crmaykish/mackerel-68k/media/images/cbr_refresh_timing.png

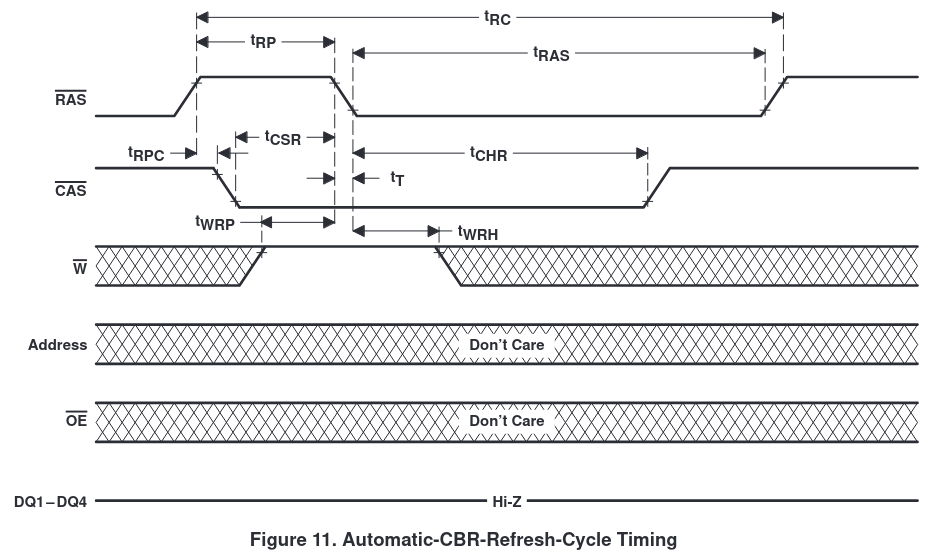
media/images/cbr_refresh_timing.png
