crmaykish/mackerel-68k/media/images/cbr_scope.png

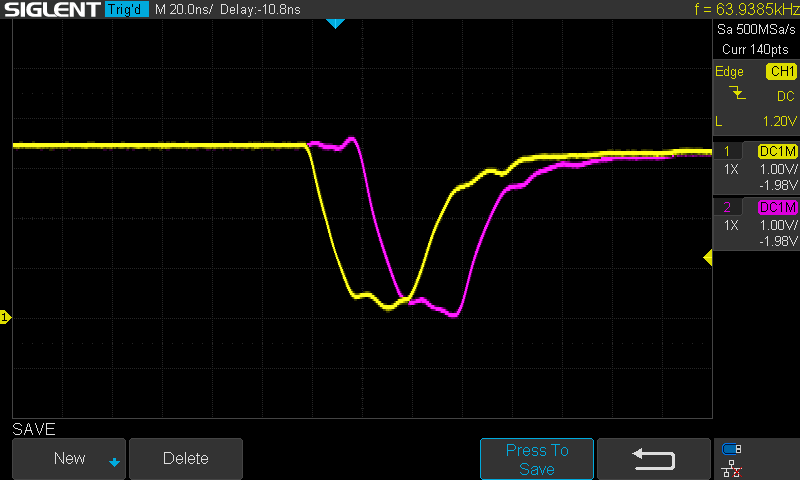
media/images/cbr_scope.png
