crmaykish/mackerel-68k/media/images/dram-cbr-refresh-simulation.png

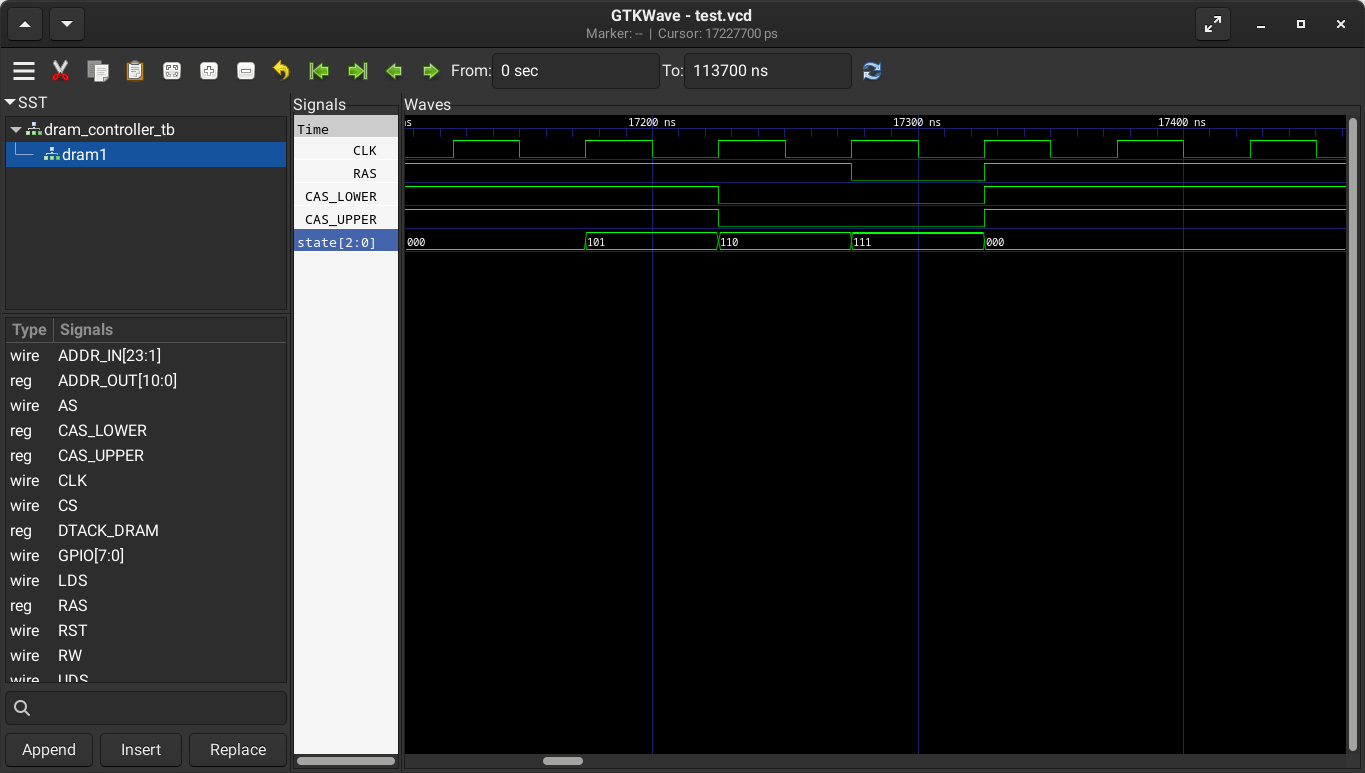
media/images/dram-cbr-refresh-simulation.png
