crmaykish/mackerel-68k/media/images/mack10_ide_proto.jpg

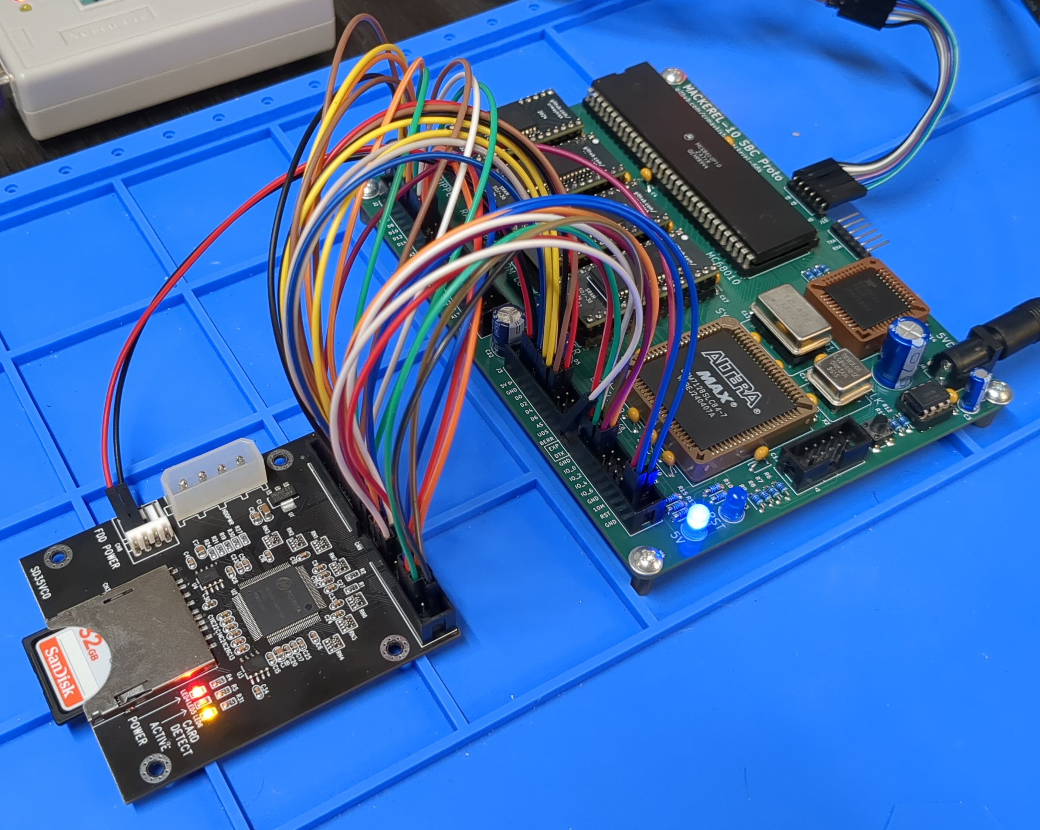
media/images/mack10_ide_proto.jpg
