crmaykish/mackerel-68k/media/images/mack-10-linux-mem-layout.png

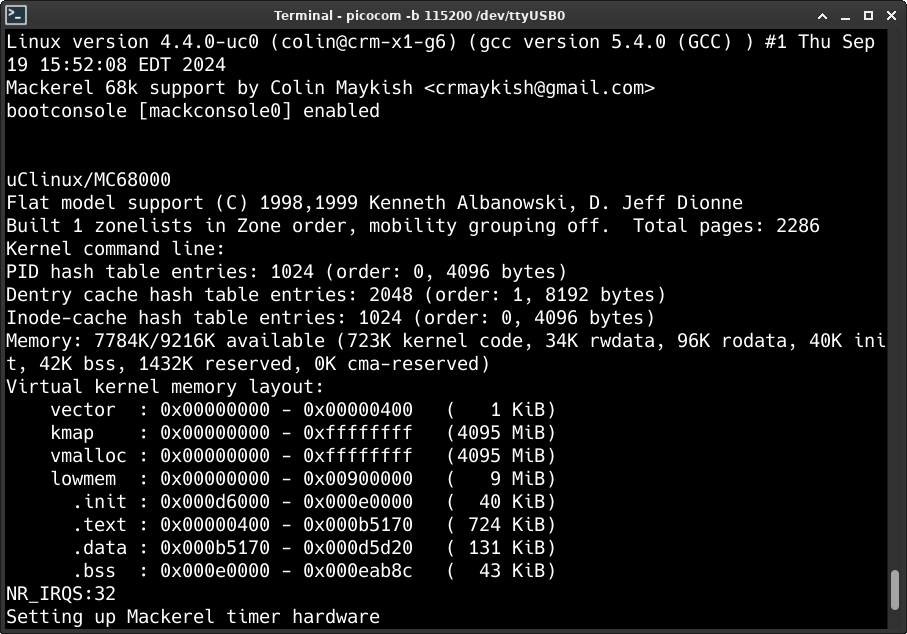
media/images/mack-10-linux-mem-layout.png
