crmaykish/mackerel-68k/media/images/mack-10-v1-routing.png

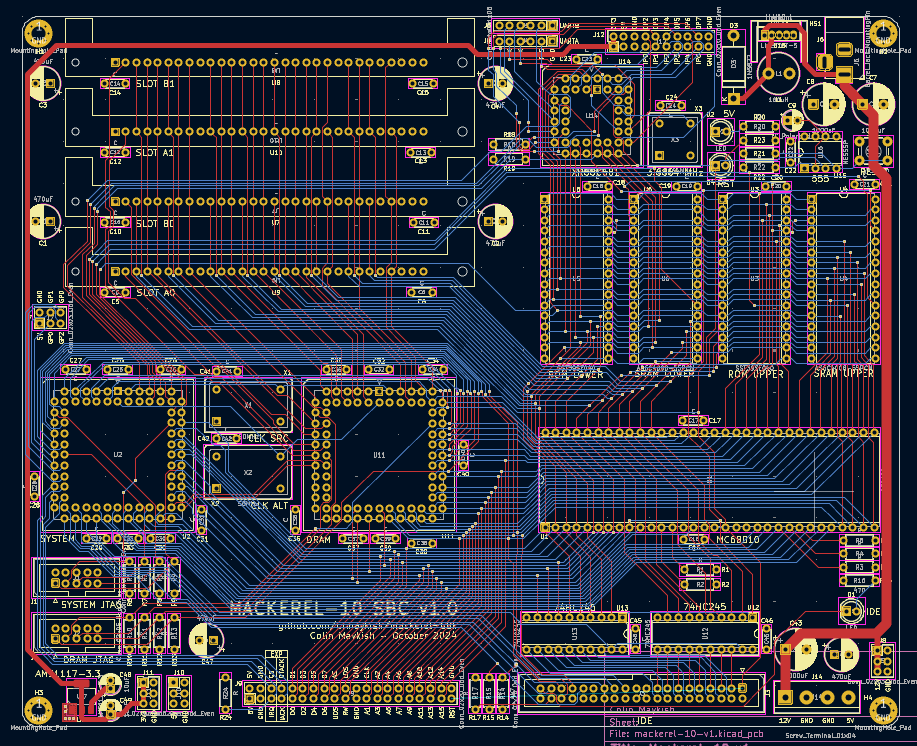
media/images/mack-10-v1-routing.png
