crmaykish/mackerel-68k/media/images/mackerel-08-rev0.jpg

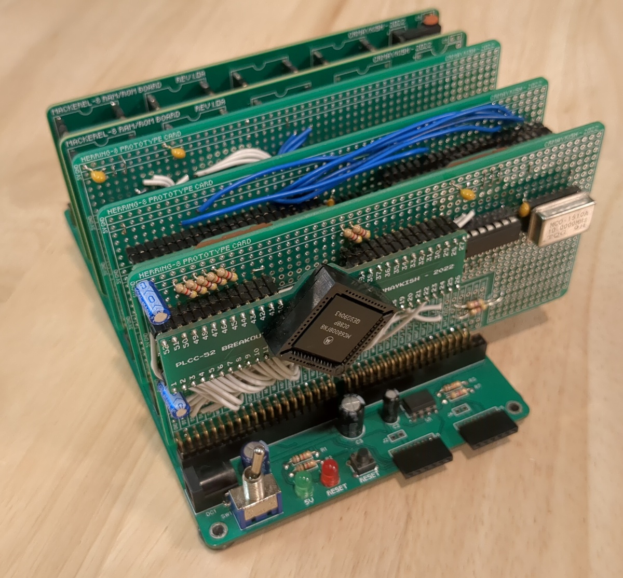
media/images/mackerel-08-rev0.jpg
