crmaykish/mackerel-68k/media/images/mackerel-08-rev1.1.jpg

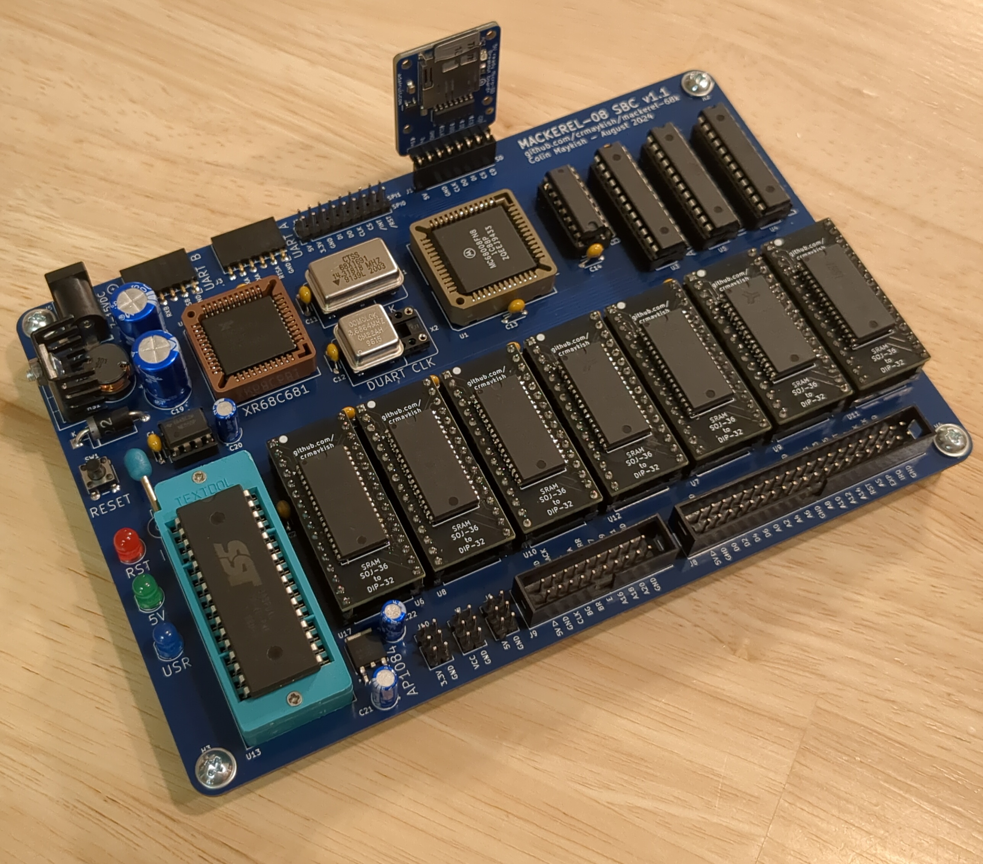
media/images/mackerel-08-rev1.1.jpg
