crmaykish/mackerel-68k/media/images/mackerel-08-sbc-v1-routing.png

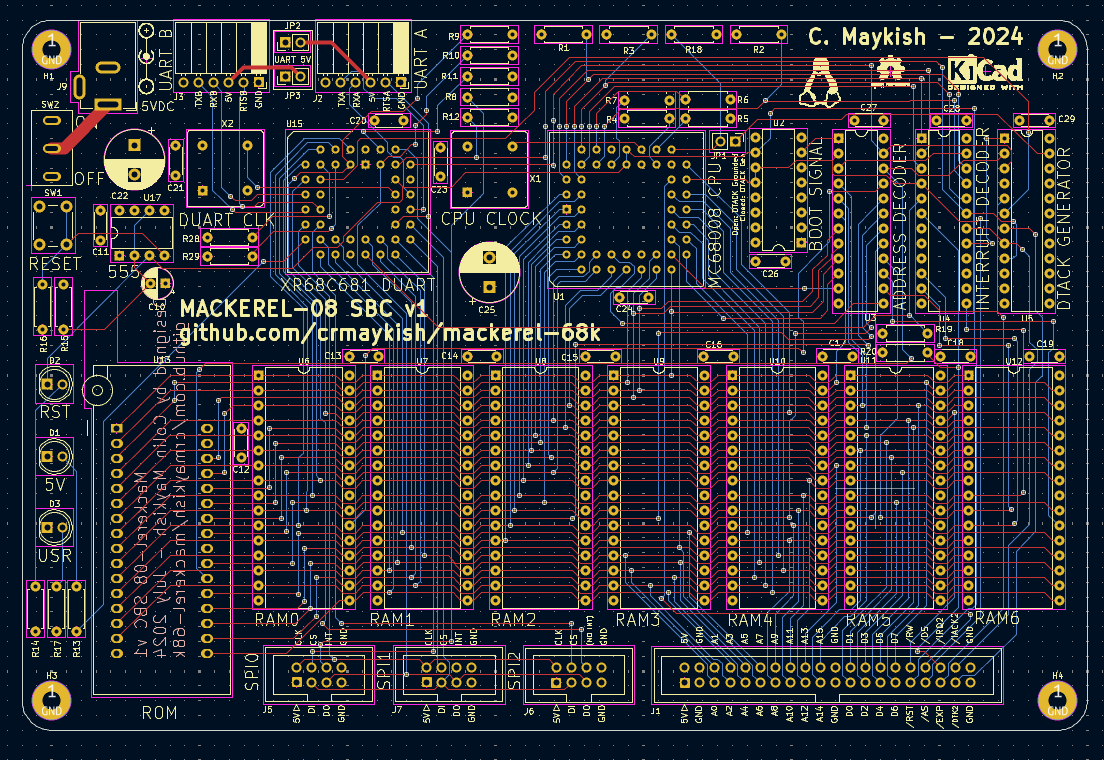
media/images/mackerel-08-sbc-v1-routing.png
