crmaykish/mackerel-68k/media/images/mackerel-08-sbc-v1.1-render.png

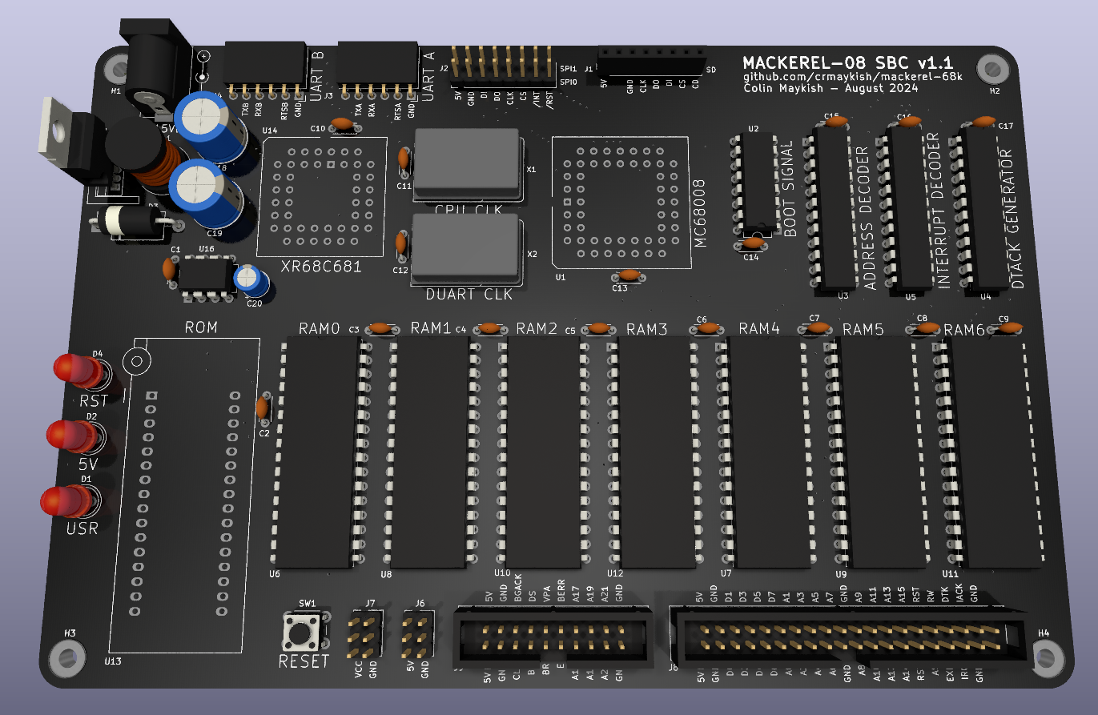
media/images/mackerel-08-sbc-v1.1-render.png
