crmaykish/mackerel-68k/media/images/mackerel-10-proto.jpg

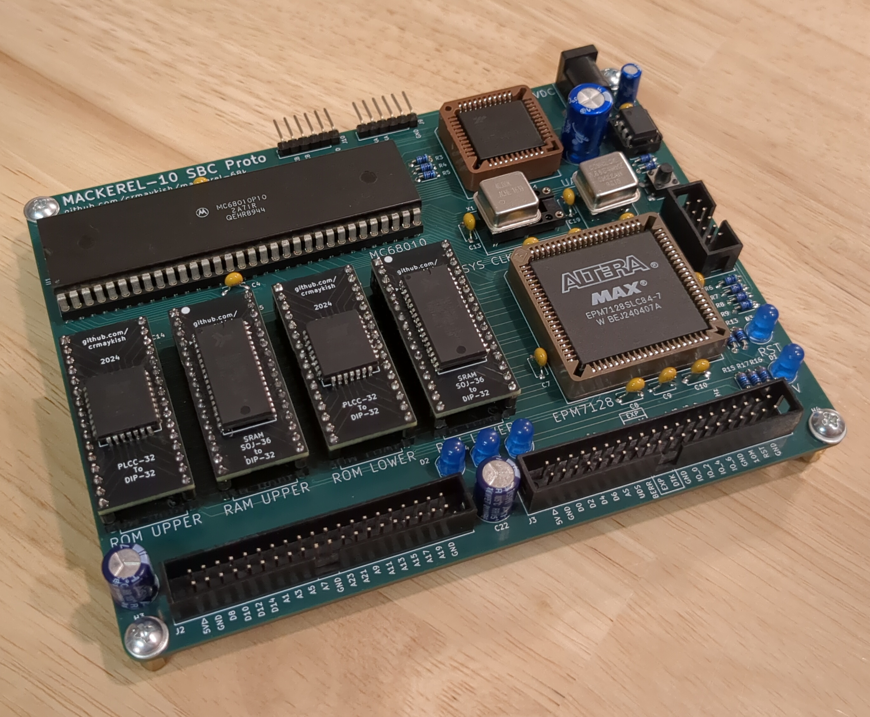
media/images/mackerel-10-proto.jpg
