crmaykish/mackerel-68k/media/images/mackerel-10-sbc-proto-render.png

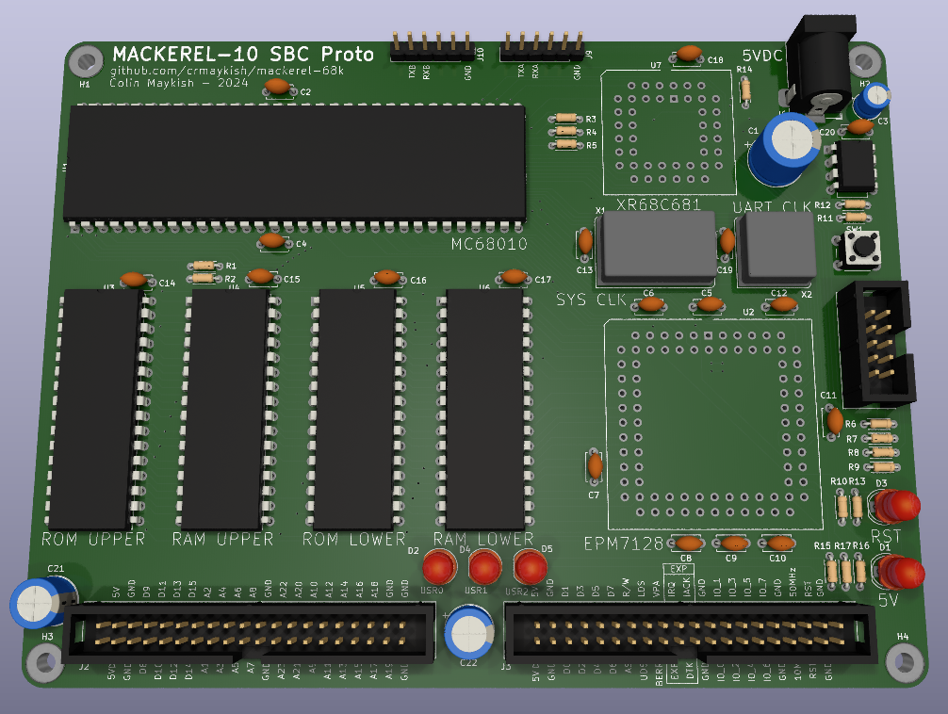
media/images/mackerel-10-sbc-proto-render.png
