crmaykish/mackerel-68k/media/images/mackerel-10-v1-with-drive.jpg

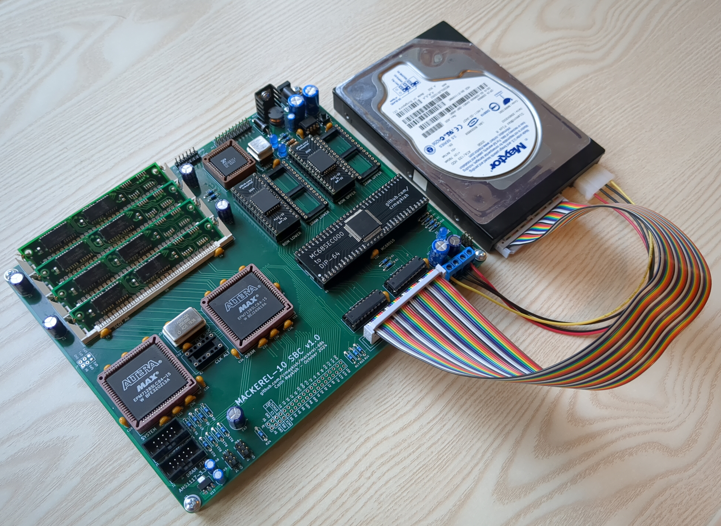
media/images/mackerel-10-v1-with-drive.jpg
