crmaykish/mackerel-68k/media/images/mackerel-30-v0.1-routing.png

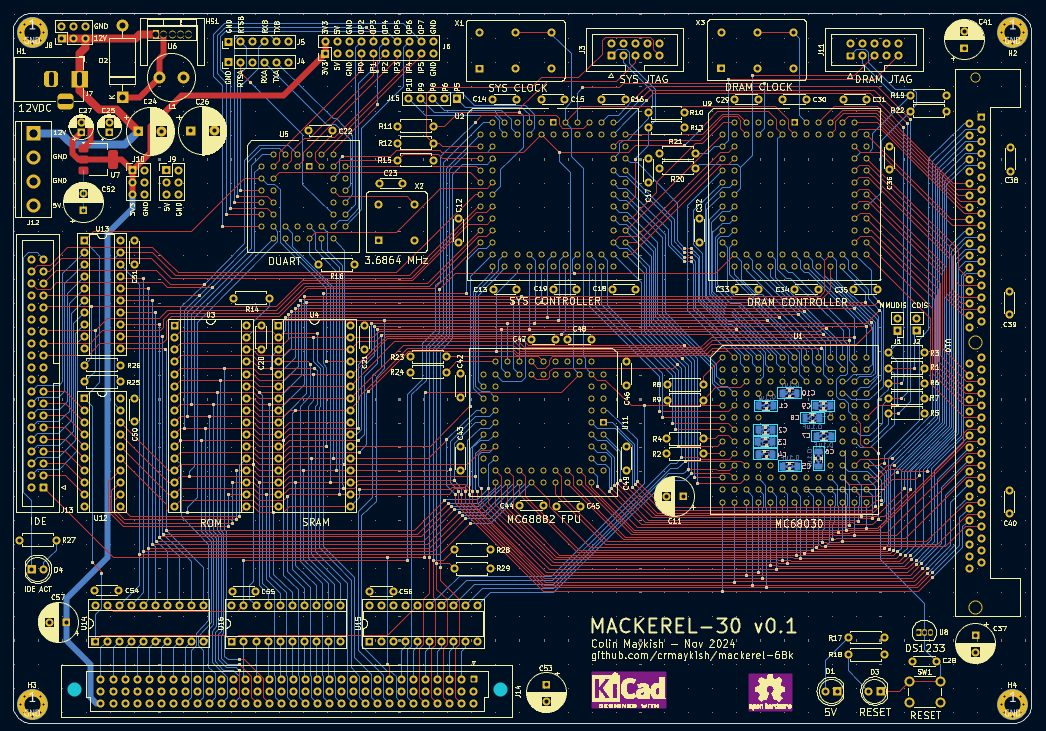
media/images/mackerel-30-v0.1-routing.png
