crmaykish/mackerel-68k/media/images/mackerel-f.png

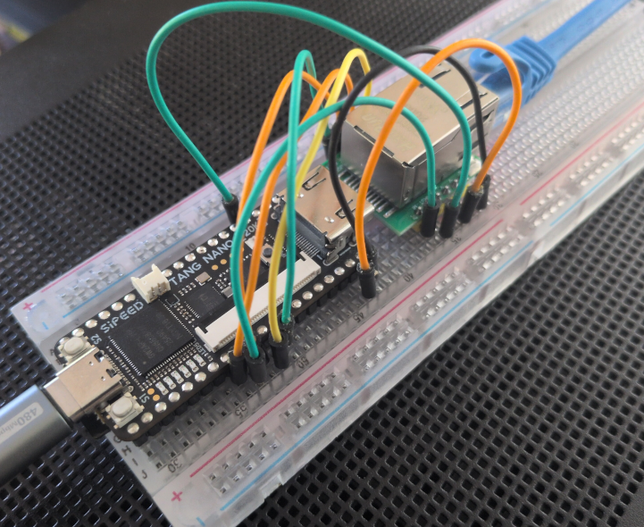
media/images/mackerel-f.png
