crmaykish/mackerel-68k/media/images/mackerel-08-sbc-v1-board-bringup.jpg

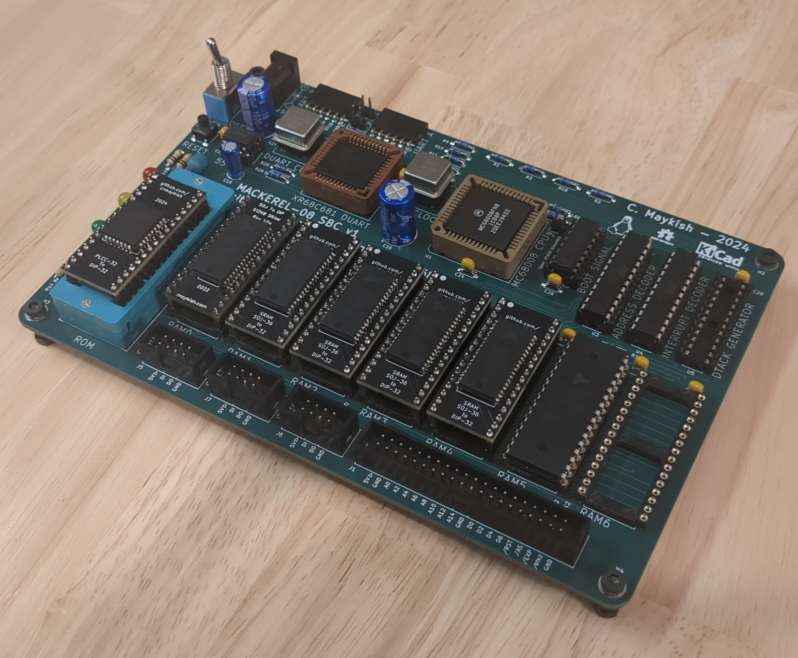
media/images/mackerel-08-sbc-v1-board-bringup.jpg
