crmaykish/mackerel-68k/media/images/mackerel-30-v0.1-bringup.jpg

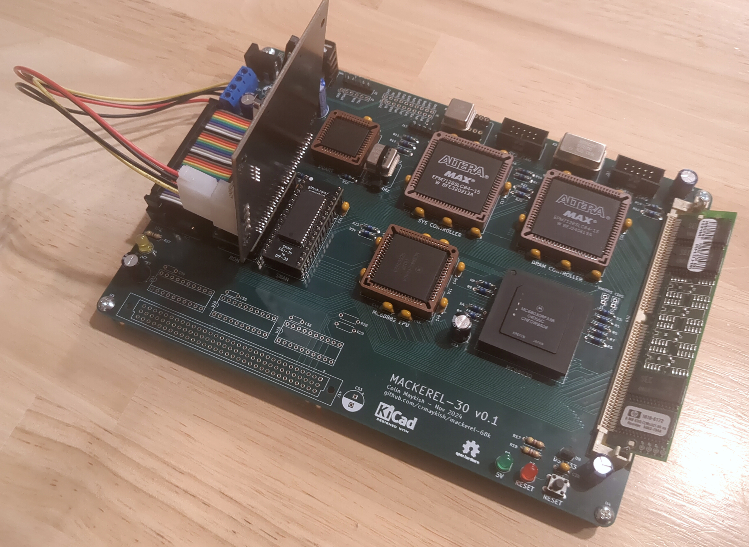
media/images/mackerel-30-v0.1-bringup.jpg
