crmaykish/mackerel-68k/pld/mackerel-30/system_controller/system_controller.v

module system_controller(
	input RST_n,
	input CLK,

	input [31:28] AH,	// Address bus (high)
	input [19:16] AM,	// Address bus (mid)
	input [3:0] AL,		// Address bus (low)

	output reg DSACK0_n, DSACK1_n,
	output BERR_n,
	output reg AVEC_n = 1'b1,
	output CIIN_n,
	output STERM_n,

	input [2:0] FC,
	output [2:0] IPL_n,
	
	input AS_n, DS_n,
	input SIZ0, SIZ1,
	input RW,
	
	output CS_ROM_n,
	output CS_SRAM_n,
	
	output CS_DRAM_n,
	input DSACK0_DRAM_n,
	input DSACK1_DRAM_n,

	output CS_FPU_n,
	input DSACK0_FPU_n,
	input DSACK1_FPU_n,
	
	output CS_DUART_n,
	output IACK_DUART_n,
	input IRQ_DUART_n,
	input DTACK_DUART_n,
	
	output IDE_BUF_n,
	output IDE_CS0_n,
	output IDE_CS1_n,
	output IDE_WR_n,
	output IDE_RD_n,
	input IDE_RDY,
	input IDE_INT,
	
	output EXP_BUF_n,
	output P5, P6, P8, P9,

	input ENC_INT_n
);

// === COMMON SIGNALS === //

// Processor is addressing CPU space
wire CPU_SPACE = (FC == 3'b111);
// Processor is responding to an interrupt
wire IACK_n = ~(CPU_SPACE && ~AS_n && AM[19:16] == 4'b1111);

// SRAM address space: 0xC0000000
wire SRAM_SPACE = (AH == 4'b1100);
// DRAM address space: 0x00000000
wire DRAM_SPACE = (AH == 4'b0000);
// ROM address space: 0xE0000000
wire ROM_SPACE = (AH == 4'b1110);
// I/O address space: 0xF0000000
wire IO_SPACE = (AH == 4'b1111);

// Coprocessor cycle — used for both CS_FPU_n and DSACK routing
wire COP_CYCLE = CPU_SPACE && ~AS_n && (AM == 4'b0010);

// Tie BERR high - bus errors will just hang the CPU
assign BERR_n = 1'b1;

// Inhibit cache for I/O
assign CIIN_n = ~(~CPU_SPACE && ~AS_n && (IO_SPACE));
assign STERM_n = 1'b1;

// === BOOT SIGNAL === //

wire BOOT;
boot_signal bs(RST_n, AS_n, BOOT);

// DUART IACK is mapped to IRQ level 5
assign IACK_DUART_n = ~(~IACK_n && AL[3:1] == 3'd5);

// === ADDRESS DECODING === //

// ROM at 0xE0000000 (mapped to 0x0000 for the first eight bus cycles)
wire ROM_EN = ~BOOT || (AH == 4'b1110);
assign CS_ROM_n = ~(~CPU_SPACE && ~AS_n && ROM_EN);

assign CS_SRAM_n = ~(BOOT && ~CPU_SPACE && ~AS_n && ~DS_n && AH == 4'b1100);

// DRAM at 0x0000_0000 - 0x7FFF_FFFF
assign CS_DRAM_n = ~(BOOT && ~CPU_SPACE && AH == 4'b0000);
// assign CS_DRAM_n = 1'b1;

// DUART at 0xF0000000
assign CS_DUART_n = ~(BOOT && ~CPU_SPACE && ~AS_n && ~DS_n && IO_SPACE && AM == 4'b0000);

// IDE CS0 at 0xF0010000
assign IDE_CS0_n = ~(BOOT && ~CPU_SPACE && IO_SPACE && AM == 4'b0001);
// IDE CS1 at 0xF0020000
assign IDE_CS1_n = ~(BOOT && ~CPU_SPACE && IO_SPACE && AM == 4'b0010);

// Timer control registers at 0xF0030000
wire CS_TIMER_n;
assign CS_TIMER_n = ~(BOOT && ~CPU_SPACE && ~AS_n && ~DS_n && IO_SPACE && AM == 4'b0011);

// IDE is selected if either CS0 or CS1 is active
wire CS_IDE_n = ~(~AS_n && (~IDE_CS0_n || ~IDE_CS1_n));

assign IDE_BUF_n = CS_IDE_n;
assign IDE_RD_n = ~(RW && ~AS_n && ~DS_n);
assign IDE_WR_n = ~(~RW && ~AS_n && ~DS_n);

// TODO: Expansion buffer currently not supported
assign EXP_BUF_n = 1'b1;

// CS_FPU_n gated by AS_n (same as COP_CYCLE) to prevent spurious assertions
// between bus cycles when FC/AM transiently pass through coprocessor values.
assign CS_FPU_n = ~COP_CYCLE;

// === WAIT STATE GENERATION === //

// PIO mode 0 minimum cycle time is 600 ns; at 24 MHz (41.7 ns/cycle) that
// requires ~14 wait clocks.  The ide_waiting pulse is held for IDE_WAIT+1
// cycles, so IDE_WAIT=14 gives 15 cycles (~625 ns)
parameter IDE_WAIT  = 14;  // IDE wait states (cycles)
parameter DUART_WAIT = 0;  // DUART wait states (cycles)

reg [3:0] ide_wait_cnt = 0;
reg [3:0] duart_wait_cnt = 0;
reg ide_waiting = 0;
reg duart_waiting = 0;

// Clocked wait-state generator
always @(posedge CLK or negedge RST_n) begin
    if (!RST_n) begin
        ide_wait_cnt <= 0;
		ide_waiting <= 0;
        duart_wait_cnt <= 0;
        duart_waiting <= 0;
    end
	else begin
        // IDE wait state logic
        if (~CS_IDE_n && ~ide_waiting) begin
            ide_wait_cnt <= 0;
            ide_waiting <= 1;
        end else if (ide_waiting && ide_wait_cnt < IDE_WAIT) begin
            ide_wait_cnt <= ide_wait_cnt + 1;
        end else if (ide_waiting && ide_wait_cnt >= IDE_WAIT) begin
            ide_waiting <= 0;
        end

        // DUART wait state logic
        if (~CS_DUART_n && ~duart_waiting) begin
            duart_wait_cnt <= 0;
            duart_waiting <= 1;
        end else if (duart_waiting && duart_wait_cnt < DUART_WAIT) begin
            duart_wait_cnt <= duart_wait_cnt + 1;
        end else if (duart_waiting && duart_wait_cnt >= DUART_WAIT) begin
            duart_waiting <= 0;
        end
    end
end

// === TIMER INTERRUPT === //
parameter integer CPU_CLK_HZ    = 24_000_000;
parameter integer TIMER_DIVIDER = CPU_CLK_HZ / 100;  // 100 Hz timer tick
reg [$clog2(TIMER_DIVIDER)-1:0] timer_cnt = 0;
reg timer_enable = 1'b0;
reg IRQ_TIMER = 1'b0;   // Timer interrupt flag

// Detect writes to enable / disable registers
wire timer_write = (~CS_TIMER_n && ~RW);  // active during write cycle
wire timer_en_write  = timer_write && (AL == 4'h0);
wire timer_dis_write = timer_write && (AL == 4'h1);

// Level 6 IACK detection (autovector) to clear pending
wire IACK_LVL6 = (~IACK_n && ~AS_n && AL[3:1] == 3'd6);

always @(posedge CLK or negedge RST_n) begin
    if (!RST_n) begin
        timer_cnt <= 0;
        timer_enable <= 1'b0;
        IRQ_TIMER <= 1'b0;
    end else begin
        // Register writes
        if (timer_en_write)
            timer_enable <= 1'b1;
        else if (timer_dis_write) begin
            timer_enable <= 1'b0;
            IRQ_TIMER <= 1'b0;
            timer_cnt <= 0;
        end

        // Counter / interrupt generation
        if (timer_enable) begin
            if (timer_cnt == TIMER_DIVIDER - 1) begin
                timer_cnt <= 0;
                IRQ_TIMER <= 1'b1;
            end else begin
                timer_cnt <= timer_cnt + 1;
            end
        end else begin
            timer_cnt <= 0;
        end

        // Clear on level 6 IACK
        if (IACK_LVL6)
            IRQ_TIMER <= 1'b0;
    end
end

// === ENC28J60 INTERRUPT (IPL 4) === //
// Edge-detecting latch: fires on falling edge of ENC_INT_n, clears on IACK
reg enc_int_prev = 1'b1;
reg IRQ_ENC      = 1'b0;
wire IACK_LVL4 = ~IACK_n && ~AS_n && AL[3:1] == 3'd4;

always @(posedge CLK or negedge RST_n) begin
    if (!RST_n) begin
        enc_int_prev <= 1'b1;
        IRQ_ENC      <= 1'b0;
    end else begin
        enc_int_prev <= ENC_INT_n;
        if (enc_int_prev && !ENC_INT_n)  // falling edge → latch
            IRQ_ENC <= 1'b1;
        else if (IACK_LVL4)              // IACK → clear
            IRQ_ENC <= 1'b0;
    end
end

// === INTERRUPT HANDLING === //

irq_encoder ie1(
	.irq1(0),
	.irq2(0),
	.irq3(IDE_INT),
	.irq4(0),   // TODO: Wire IRQ_ENC when ENC28J60 is installed
	.irq5(~IRQ_DUART_n),
	.irq6(IRQ_TIMER),
	.irq7(0),
	.ipl0_n(IPL_n[0]),
	.ipl1_n(IPL_n[1]),
	.ipl2_n(IPL_n[2])
);

// Autovector the non-DUART interrupts
always @(*) begin
    if (~IACK_n && IACK_DUART_n && ~AS_n)
        AVEC_n = 1'b0;
    else
        AVEC_n = 1'b1;
end

// === DSACK GENERATION === //
always @(*) begin
    // Handle interrupt acknowledge cycles
    if (~IACK_n) begin
        if (~IACK_DUART_n) begin
            DSACK0_n = 1'b0;
            DSACK1_n = 1'b1;
        end else begin
            // Autovector
            DSACK0_n = 1'b0;
            DSACK1_n = 1'b1;
        end
    end
    else if (~CS_DRAM_n) begin
        // Gate DRAM DSACK with AS
        if (~AS_n) begin
            DSACK0_n = DSACK0_DRAM_n;
            DSACK1_n = DSACK1_DRAM_n;
        end else begin
            DSACK0_n = 1'b1;
            DSACK1_n = 1'b1;
        end
    end
    else if (~CS_IDE_n) begin
        // Insert IDE wait states before asserting DSACK
        if (ide_waiting) begin
            DSACK0_n = 1'b1;
            DSACK1_n = 1'b1;
        end
        else begin
            DSACK0_n = 1'b1;
            DSACK1_n = 1'b0;
        end
    end
    else if (~CS_DUART_n) begin
        // Insert DUART wait states before asserting DSACK
        if (duart_waiting) begin
            DSACK0_n = 1'b1;
            DSACK1_n = 1'b1;
        end
        else begin
            DSACK0_n = 1'b0;
            DSACK1_n = 1'b1;
        end
    end
    else if (~CS_TIMER_n) begin
        // Timer registers respond immediately
        DSACK0_n = 1'b0;
        DSACK1_n = 1'b1;
    end
    else if (~CS_ROM_n || ~CS_SRAM_n) begin
        DSACK0_n = 1'b0;
        DSACK1_n = 1'b1;
    end
    else if (~CS_FPU_n) begin
        DSACK0_n = DSACK0_FPU_n;
        DSACK1_n = DSACK1_FPU_n;
    end
    else begin
        DSACK0_n = 1'b1;
        DSACK1_n = 1'b1;
    end
end

endmodule
