crmaykish/mackerel-68k/firmware/fat16.c

#include <stdio.h>
#include <string.h>
#include "fat16.h"
#include "term.h"
#include "console.h"

fat16_read_sector_f read_sector = NULL;

// Start LBA of the FAT16 partition. Defaults to 2048 (the conventional 1 MB offset)
static uint32_t fat16_part_lba = 2048;

uint32_t fat16_part_start(void) { return fat16_part_lba; }

// Read the MBR (LBA 0) and locate the first FAT16 partition, setting the start
// LBA used by the rest of the library. Returns 0 if one was found, -1 otherwise
int fat16_find_partition(void)
{
    if (read_sector == NULL)
        return -1;

    uint8_t mbr[512];
    if (read_sector(0, mbr, 1) != 0)
        return -1;
    if (mbr[510] != 0x55 || mbr[511] != 0xAA)   // boot signature
        return -1;

    for (int i = 0; i < 4; i++)
    {
        const uint8_t *e = mbr + 0x1BE + i * 16;
        uint8_t type = e[4];
        // FAT16: 0x04 (<32MB), 0x06 (FAT16B), 0x0E (FAT16 LBA)
        if (type == 0x04 || type == 0x06 || type == 0x0E)
        {
            fat16_part_lba = (uint32_t)e[8] | ((uint32_t)e[9] << 8) | ((uint32_t)e[10] << 16) | ((uint32_t)e[11] << 24);
            return 0;
        }
    }
    return -1;
}

void bswap_boot_sector(fat16_boot_sector_t *b)
{
    if (b == NULL)
        return;

    b->bytes_per_sector = bswap16(b->bytes_per_sector);
    b->reserved_sectors = bswap16(b->reserved_sectors);
    b->root_entries = bswap16(b->root_entries);
    b->total_sectors_16 = bswap16(b->total_sectors_16);
    b->fat_size_16 = bswap16(b->fat_size_16);
    b->sectors_per_track = bswap16(b->sectors_per_track);
    b->heads = bswap16(b->heads);
    b->hidden_sectors = bswap32(b->hidden_sectors);
    b->total_sectors_32 = bswap32(b->total_sectors_32);
    b->volume_id = bswap32(b->volume_id);
    b->boot_sector_signature = bswap16(b->boot_sector_signature);
}

void bswap_dir_entry(fat16_dir_entry_t *d)
{
    if (d == NULL)
        return;

    d->creation_time = bswap16(d->creation_time);
    d->creation_date = bswap16(d->creation_date);
    d->last_access_date = bswap16(d->last_access_date);
    d->first_cluster_high = bswap16(d->first_cluster_high);
    d->modification_time = bswap16(d->modification_time);
    d->modification_date = bswap16(d->modification_date);
    d->first_cluster_low = bswap16(d->first_cluster_low);
    d->file_size = bswap32(d->file_size);
}

int fat16_init(fat16_read_sector_f read_sector_fun)
{
    if (read_sector_fun)
    {
        read_sector = read_sector_fun;
        return 0;
    }

    return -1;
}

void fat16_read_boot_sector(uint32_t starting_sector, fat16_boot_sector_t *buffer)
{
    read_sector(starting_sector, (uint8_t *)(buffer), 1);
    bswap_boot_sector(buffer);
}

void fat16_print_boot_sector_info(fat16_boot_sector_t *buffer)
{
    printf("\r\nBoot sector info:\r\n");
    printf("Bytes per sector: %u\n", buffer->bytes_per_sector);
    printf("Sectors per cluster: %u\n", buffer->sectors_per_cluster);
    printf("Reserved sectors: %u\n", buffer->reserved_sectors);
    printf("FAT count: %u\n", buffer->num_fats);
    printf("Root directory entries: %u\n", buffer->root_entries);
    printf("Total sectors: %u\n", buffer->total_sectors_16);
    printf("FAT size (sectors): %u\n", buffer->fat_size_16);
    printf("Sectors per track: %u\n", buffer->sectors_per_track);
    printf("Head count: %u\n", buffer->heads);
    printf("Hidden sectors: %lu\n", buffer->hidden_sectors);
    printf("Total sectors (large): %lu\n", buffer->total_sectors_32);
}

int fat16_list_files(fat16_boot_sector_t *boot_sector, fat16_dir_entry_t files_list[])
{
    if (read_sector == NULL)
    {
        printf("read_sector function pointer is NULL. Call fat16_init() first\r\n");
        return -1;
    }

    if (boot_sector == NULL)
    {
        printf("boot_sector is NULL\r\n");
        return -1;
    }

    int valid_files = 0;

    uint32_t root_dir_sector = fat16_part_lba + boot_sector->reserved_sectors + (boot_sector->num_fats * boot_sector->fat_size_16);
    uint8_t buffer[512];

    read_sector(root_dir_sector, buffer, 1);

    // TODO: this 16 value should be determined by the root directory count in the boot sector
    // After 16 entries, a new sector needs to be read (I think)
    for (int i = 0; i < 16; i++)
    {
        fat16_dir_entry_t *entry = (fat16_dir_entry_t *)(buffer + i * 32);

        bswap_dir_entry(entry);

        // Check if the entry is free (0x00) or deleted (0xE5)
        if (entry->filename[0] == 0x00 || entry->filename[0] == 0xE5)
        {
            continue; // Skip empty or deleted entries
        }

        // Check if the entry represents a valid file or directory
        if (entry->attributes & 0x10)
        {
            // This is a directory (attribute 0x10)
            continue;
        }

        memcpy(&files_list[valid_files], entry, 32);
        valid_files++;
    }

    return valid_files;
}

void fat16_get_file_name(fat16_dir_entry_t *dir_entry, char *filename)
{
    if (dir_entry == NULL)
    {
        return;
    }

    if (filename == NULL)
    {
        return;
    }

    memset(filename, ' ', 13);

    // Copy the name
    strncpy(filename, (char *)dir_entry->filename, 8);
    // Add a dot between the name and extension
    filename[8] = '.';
    // Copy the extension
    strncpy(filename + 9, (char *)dir_entry->extension, 3);

    filename[12] = 0; // Null-terminate the string
}

// Function to get the next cluster from the FAT
uint16_t get_fat_entry(fat16_boot_sector_t *boot_sector, uint16_t cluster)
{
    static uint32_t cached_sector = (uint32_t)-1;
    static uint8_t fat_buffer[1024]; // Make sure this is large enough for your largest sector size

    uint32_t fat_offset = cluster * 2;
    uint32_t fat_sector = boot_sector->hidden_sectors + boot_sector->reserved_sectors + (fat_offset / boot_sector->bytes_per_sector);
    uint32_t fat_entry_offset = fat_offset % boot_sector->bytes_per_sector;

    // Only read if not already cached
    if (fat_sector != cached_sector) {
        if (read_sector(fat_sector, fat_buffer, 1) != 0)
            return 0xFFFF;  // treat read failure as end-of-chain
        cached_sector = fat_sector;
    }

    uint16_t next_cluster = (fat_buffer[fat_entry_offset] | (fat_buffer[fat_entry_offset + 1] << 8)) & 0xFFFF;
    return next_cluster;
}

int fat16_read_file(fat16_boot_sector_t *boot_sector, uint16_t starting_cluster, uint8_t *buffer, uint32_t buffer_size)
{
    uint32_t buffer_index = 0;
    uint16_t current_cluster = starting_cluster;

    // Calculate the first sector of the cluster
    uint32_t sector_size = boot_sector->bytes_per_sector;
    uint32_t sectors_per_cluster = boot_sector->sectors_per_cluster;

    // Progress reporting
    uint32_t pct_step = buffer_size / 100;
    if (pct_step == 0)
        pct_step = 1;
    int last_pct = -1;

    // Hide the cursor while the progress bar redraws to keep it from
    // flickering across the bar. Re-enabled on every exit path below.
    term_cursor_set_vis(false);

    uint32_t root_dir_sectors = (boot_sector->root_entries * 32 + sector_size - 1) / sector_size;

    while (current_cluster != 0xFFFF && buffer_index < buffer_size)
    {
        // printf("current cluster: %u\r\n", current_cluster);

        uint32_t first_sector_of_cluster = root_dir_sectors + fat16_part_lba + (current_cluster - 2) * sectors_per_cluster + boot_sector->reserved_sectors + (boot_sector->num_fats * boot_sector->fat_size_16);

        // Read the sectors of the current cluster into the buffer
        uint32_t remaining = buffer_size - buffer_index;
        uint32_t cluster_bytes = (uint32_t)sectors_per_cluster * sector_size;

        if (remaining >= cluster_bytes)
        {
            // Whole cluster fits — one multi-sector read straight into destination
            if (read_sector(first_sector_of_cluster, buffer + buffer_index, sectors_per_cluster) != 0)
            {
                term_cursor_set_vis(true);
                return -1;
            }
            buffer_index += cluster_bytes;
        }
        else
        {
            // Partial cluster at end of file — fall back to sector by sector
            for (uint32_t i = 0; i < sectors_per_cluster && buffer_index < buffer_size; i++)
            {
                uint32_t rem = buffer_size - buffer_index;
                if (rem >= sector_size)
                {
                    if (read_sector(first_sector_of_cluster + i, buffer + buffer_index, 1) != 0)
                    {
                        term_cursor_set_vis(true);
                        return -1;
                    }
                    buffer_index += sector_size;
                }
                else
                {
                    uint8_t sector_buffer[sector_size];
                    if (read_sector(first_sector_of_cluster + i, sector_buffer, 1) != 0)
                    {
                        term_cursor_set_vis(true);
                        return -1;
                    }
                    memcpy(buffer + buffer_index, sector_buffer, rem);
                    buffer_index += rem;
                }
            }
        }

        // Redraw the progress bar only when the percentage changes.
        int pct = buffer_index / pct_step;
        if (pct > 100)
            pct = 100;
        if (pct != last_pct)
        {
            last_pct = pct;
            term_progress_bar(pct);
        }

        // Get the next cluster from the FAT
        current_cluster = get_fat_entry(boot_sector, current_cluster);
    }

    term_progress_bar(100);
    console_putc('\r');
    console_putc('\n');
    term_cursor_set_vis(true);

    return buffer_index; // Returns the number of bytes read
}
