crmaykish/mackerel-68k/firmware/ide.c

#ifndef MACKEREL_08
#include "ide.h"
#include "mackerel.h"
#include <stdio.h>


#ifdef MACKEREL_30
static const uint8_t bit_reverse_table[256] = {
    0x00, 0x80, 0x40, 0xC0, 0x20, 0xA0, 0x60, 0xE0, 0x10, 0x90, 0x50, 0xD0, 0x30, 0xB0, 0x70, 0xF0,
    0x08, 0x88, 0x48, 0xC8, 0x28, 0xA8, 0x68, 0xE8, 0x18, 0x98, 0x58, 0xD8, 0x38, 0xB8, 0x78, 0xF8,
    0x04, 0x84, 0x44, 0xC4, 0x24, 0xA4, 0x64, 0xE4, 0x14, 0x94, 0x54, 0xD4, 0x34, 0xB4, 0x74, 0xF4,
    0x0C, 0x8C, 0x4C, 0xCC, 0x2C, 0xAC, 0x6C, 0xEC, 0x1C, 0x9C, 0x5C, 0xDC, 0x3C, 0xBC, 0x7C, 0xFC,
    0x02, 0x82, 0x42, 0xC2, 0x22, 0xA2, 0x62, 0xE2, 0x12, 0x92, 0x52, 0xD2, 0x32, 0xB2, 0x72, 0xF2,
    0x0A, 0x8A, 0x4A, 0xCA, 0x2A, 0xAA, 0x6A, 0xEA, 0x1A, 0x9A, 0x5A, 0xDA, 0x3A, 0xBA, 0x7A, 0xFA,
    0x06, 0x86, 0x46, 0xC6, 0x26, 0xA6, 0x66, 0xE6, 0x16, 0x96, 0x56, 0xD6, 0x36, 0xB6, 0x76, 0xF6,
    0x0E, 0x8E, 0x4E, 0xCE, 0x2E, 0xAE, 0x6E, 0xEE, 0x1E, 0x9E, 0x5E, 0xDE, 0x3E, 0xBE, 0x7E, 0xFE,
    0x01, 0x81, 0x41, 0xC1, 0x21, 0xA1, 0x61, 0xE1, 0x11, 0x91, 0x51, 0xD1, 0x31, 0xB1, 0x71, 0xF1,
    0x09, 0x89, 0x49, 0xC9, 0x29, 0xA9, 0x69, 0xE9, 0x19, 0x99, 0x59, 0xD9, 0x39, 0xB9, 0x79, 0xF9,
    0x05, 0x85, 0x45, 0xC5, 0x25, 0xA5, 0x65, 0xE5, 0x15, 0x95, 0x55, 0xD5, 0x35, 0xB5, 0x75, 0xF5,
    0x0D, 0x8D, 0x4D, 0xCD, 0x2D, 0xAD, 0x6D, 0xED, 0x1D, 0x9D, 0x5D, 0xDD, 0x3D, 0xBD, 0x7D, 0xFD,
    0x03, 0x83, 0x43, 0xC3, 0x23, 0xA3, 0x63, 0xE3, 0x13, 0x93, 0x53, 0xD3, 0x33, 0xB3, 0x73, 0xF3,
    0x0B, 0x8B, 0x4B, 0xCB, 0x2B, 0xAB, 0x6B, 0xEB, 0x1B, 0x9B, 0x5B, 0xDB, 0x3B, 0xBB, 0x7B, 0xFB,
    0x07, 0x87, 0x47, 0xC7, 0x27, 0xA7, 0x67, 0xE7, 0x17, 0x97, 0x57, 0xD7, 0x37, 0xB7, 0x77, 0xF7,
    0x0F, 0x8F, 0x4F, 0xCF, 0x2F, 0xAF, 0x6F, 0xEF, 0x1F, 0x9F, 0x5F, 0xDF, 0x3F, 0xBF, 0x7F, 0xFF};
#endif

// Reverse the order of the low 8-bits in a 16-bit number
uint16_t reverse_lowest_8_bits(uint16_t num)
{
    uint8_t low_bits = num & 0xFF;

    uint8_t reversed_low_bits = 0;
    for (int i = 0; i < 8; i++)
    {
        reversed_low_bits |= ((low_bits >> i) & 1) << (7 - i);
    }

    return (num & 0xFF00) | reversed_low_bits;
}

void read_sector_internal(uint16_t *buf)
{
    for (uint16_t i = 0; i < 256; i++)
    {
        // IDE_wait_for_data_ready();   // needed at higher speeds?
        buf[i] = MEM16(IDE_DATA);

#ifdef MACKEREL_30
        buf[i] = (buf[i] & 0xFF00) | bit_reverse_table[buf[i] & 0xFF];
#endif
    }
}

// polls !BSY && DRDY per ATA spec — BSY must clear before task-file registers are valid
bool IDE_wait_for_device_ready()
{
    for (uint32_t i = 0; i < IDE_TIMEOUT_READY; i++)
    {
        uint8_t status = MEM(IDE_STATUS);
        if ((status & (IDE_SR_BSY | IDE_SR_DRDY)) == IDE_SR_DRDY)
            return true;
    }
    printf("IDE timeout waiting for device ready\r\n");
    return false;
}

// returns false on timeout; also bails early if the drive signals ERR/DF
bool IDE_wait_for_data_ready()
{
    for (uint32_t i = 0; i < IDE_TIMEOUT_DRQ; i++)
    {
        uint8_t status = MEM(IDE_STATUS);
        if (status & IDE_SR_DRQ)
            return true;
        if (status & (IDE_SR_ERR | IDE_SR_DF))
            return false;
    }
    printf("IDE timeout waiting for data ready\r\n");
    return false;
}

// NOTE: limited to 24-bit LBA addressing (~8 GB)
// count: 1-255 sectors per command (0 means 256 per ATA spec, not supported here)
int IDE_read_sectors(uint16_t *buf, uint32_t lba, uint8_t count)
{
    // verify BSY clear and DRDY set before touching task-file registers
    if (!IDE_wait_for_device_ready())
        return -1;

    MEM(IDE_DRIVE_SEL) = 0xE0;
    MEM(IDE_SECTOR_COUNT) = count;
    MEM(IDE_SECTOR_START) = (uint8_t)(lba & 0xFF);
    MEM(IDE_LBA_MID)      = (uint8_t)((lba >> 8) & 0xFF);
    MEM(IDE_LBA_HIGH)     = (uint8_t)((lba >> 16) & 0xFF);
    MEM(IDE_COMMAND)      = IDE_CMD_READ_SECTOR;

    for (uint8_t s = 0; s < count; s++)
    {
        if (!IDE_wait_for_data_ready())
        {
            printf("IDE DRQ timeout at LBA %lu sector %u\r\n", lba, s);
            return -1;
        }

        read_sector_internal(buf + (uint32_t)s * 256);

        // check ERR/DF after each sector's data is transferred
        uint8_t status = MEM(IDE_STATUS);
        if (status & (IDE_SR_ERR | IDE_SR_DF))
        {
            uint8_t err = MEM(IDE_ERROR);
            printf("IDE error at LBA %lu sector %u: STATUS=0x%02X ERR=0x%02X\r\n",
                   lba, s, status, err);
            return -1;
        }
    }

    return 0;
}

int IDE_read_sector(uint16_t *buf, uint32_t lba)
{
    return IDE_read_sectors(buf, lba, 1);
}

void IDE_device_info(uint16_t *buf)
{
    printf("Reading IDE device info...\r\n");
    MEM(IDE_DRIVE_SEL) = 0xE0;
    if (!IDE_wait_for_device_ready())
    {
        printf("IDE identify timeout (device not ready)\r\n");
        return;
    }
    MEM(IDE_COMMAND) = IDE_CMD_IDENTIFY;
    if (!IDE_wait_for_data_ready())
    {
        printf("IDE identify timeout (no DRQ)\r\n");
        return;
    }
    read_sector_internal(buf);

    // Model
    printf("Model: ");
    for (int i = 27; i <= 46; i++)
    {
        printf("%c%c", (char)((buf[i] & 0x00FF)), (char)((buf[i] & 0xFF00) >> 8));
    }

    printf("\r\n");

    // Version
    printf("Version: ");
    for (int i = 23; i <= 26; i++)
    {
        printf("%c%c", (char)((buf[i] & 0x00FF)), (char)((buf[i] & 0xFF00) >> 8));
    }

    printf("\r\n");

    // Serial number
    printf("Serial number: ");
    for (int i = 10; i <= 19; i++)
    {
        printf("%c%c", (char)((buf[i] & 0x00FF)), (char)((buf[i] & 0xFF00) >> 8));
    }

    printf("\r\n");
}

void IDE_reset()
{
    // Pulse SRST in Device Control per ATA spec. Min hold time is 5 µs.
    MEM(IDE_DEVICE_CONTROL) = IDE_DC_SRST;
    sleep_us(10);
    MEM(IDE_DEVICE_CONTROL) = 0x00;
    if (!IDE_wait_for_device_ready())
        printf("IDE reset timeout\r\n");
}

#endif // MACKEREL_08
