crmaykish/mackerel-68k/firmware/ide.h

#ifndef IDE_H_
#define IDE_H_

#ifndef MACKEREL_08

#include <stdbool.h>
#include "mackerel.h"

// IDE command block registers (CS0)
#define IDE_DATA         IDE_BASE + 0x00
#define IDE_ERROR        IDE_BASE + 0x02  // read
#define IDE_FEATURE      IDE_BASE + 0x02  // write
#define IDE_SECTOR_COUNT IDE_BASE + 0x04
#define IDE_SECTOR_START IDE_BASE + 0x06
#define IDE_LBA_MID      IDE_BASE + 0x08
#define IDE_LBA_HIGH     IDE_BASE + 0x0A
#define IDE_DRIVE_SEL    IDE_BASE + 0x0C
#define IDE_STATUS       IDE_BASE + 0x0E
#define IDE_COMMAND      IDE_BASE + 0x0E

// IDE control block registers (CS1)
#define IDE_DEVICE_CONTROL IDE_CTL_BASE + 0x0C  // write: Device Control (nIEN, SRST)
#define IDE_ALT_STATUS     IDE_CTL_BASE + 0x0C  // read:  Alternate Status (no IRQ clear)

// Device Control bits
#define IDE_DC_SRST 0x04  // software reset
#define IDE_DC_NIEN 0x02  // disable drive interrupts

// IDE commands
#define IDE_CMD_RESET 0x08
#define IDE_CMD_READ_SECTOR 0x20
#define IDE_CMD_WRITE_SECTOR 0x30
#define IDE_CMD_IDENTIFY 0xEC
#define IDE_CMD_SET_FEATURES 0xEF

// Status register bits
#define IDE_SR_BSY 0x80  // Busy
#define IDE_SR_DRDY 0x40 // Drive ready
#define IDE_SR_DF 0x20   // Drive write fault
#define IDE_SR_DSC 0x10  // Drive seek complete
#define IDE_SR_DRQ 0x08  // Data request ready
#define IDE_SR_CORR 0x04 // Corrected data
#define IDE_SR_IDX 0x02  // Index
#define IDE_SR_ERR 0x01  // Error

// Timeout iteration counts (rough calibration at 24 MHz, ~333 ns/iter)
#define IDE_TIMEOUT_READY 2000000  // ~500 ms
#define IDE_TIMEOUT_DRQ    500000  // ~125 ms per sector

bool IDE_wait_for_device_ready();

bool IDE_wait_for_data_ready();

int IDE_read_sector(uint16_t *buf, uint32_t lba);

int IDE_read_sectors(uint16_t *buf, uint32_t lba, uint8_t count);

void IDE_device_info(uint16_t *buf);

void IDE_reset();

#endif // MACKEREL_08
#endif
