crmaykish/mackerel-68k/firmware/sd.h

#ifndef SD_H
#define SD_H

#include <stdbool.h>
#include "mackerel.h"
#include "spi.h"

#define CS_SD CS2   // Use CS0 for the SD card

// Setup the SD card interface
// Return true on success, false on error
bool sd_init();

// Send a 6 byte command to the SD card
// Returns the first byte of the response
uint8_t sd_command(uint8_t command[6]);

// Read a single block of SD card data into the block pointer
void sd_read(uint32_t block_num, uint8_t *block);

// Read num_blocks consecutive blocks into buf using CMD18 (multi-block read).
// More efficient than calling sd_read() in a loop for large transfers.
// Returns true on success.
bool sd_read_blocks(uint32_t start_block, uint32_t num_blocks, uint8_t *buf);

#endif
